keebio/iris-case/iris-switch-plate_left.dxf

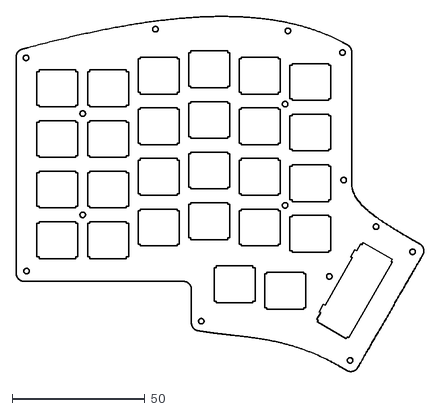
[picture p18: CAD file, 2018-07-17]
iris-switch-plate_left.dxf
153.5 x 133.7
