keebio/iris-case/rev2-only/Iris Middle Tented - Two Piece.stl

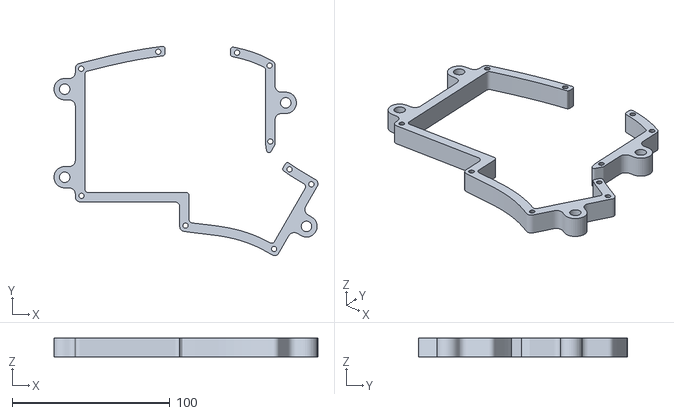
[picture p19: CAD file, 2018-10-11]
rev2-only/Iris Middle Tented - Two Piece.stl
167.2 x 132.5 x 12.0
