keebio/iris-case/phoenix-edition-PE/Iris PE Top Shell for 1.5mm plate.stl

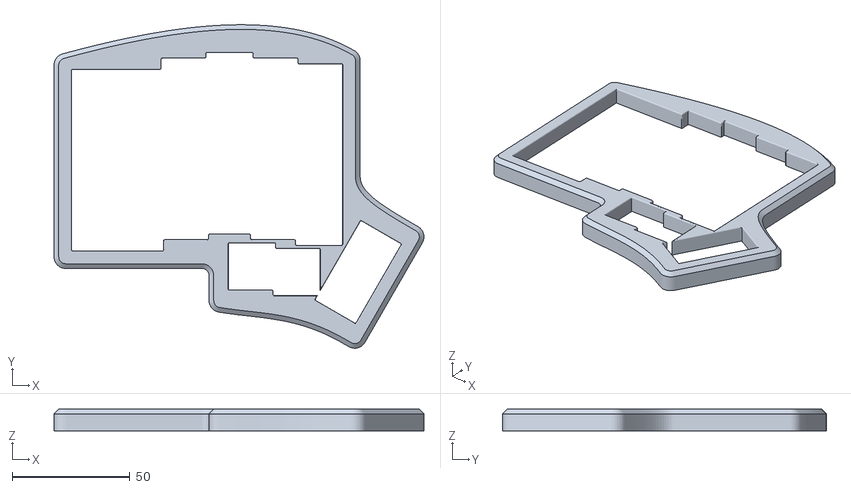
[picture p20: CAD file, 2022-03-10]
phoenix-edition-PE/Iris PE Top Shell for 1.5mm plate.stl
157.4 x 137.7 x 9.30
