keebio/iris-case/rev2-only/Iris R2 Middle Layer - Two Piece.stl

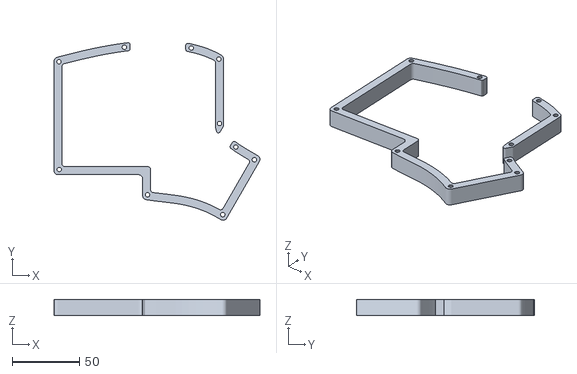
[picture p21: CAD file, 2018-10-11]
rev2-only/Iris R2 Middle Layer - Two Piece.stl
153.7 x 132.5 x 12.0
