keebio/iris-case/rev2-only/iris-rev2-bottom_right.dxf

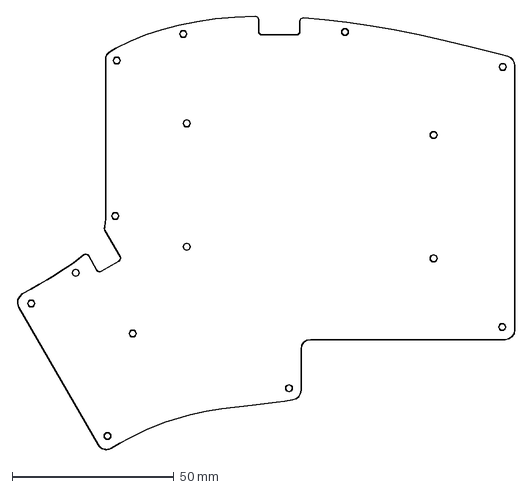
[picture p23: CAD file, 2018-07-17]
rev2-only/iris-rev2-bottom_right.dxf
153.9 x 133.7 mm
