keebio/iris-case/phoenix-edition-PE/Iris PE Middle Layer - Ergodox Tent Kit for 1.5mm Plate.stl

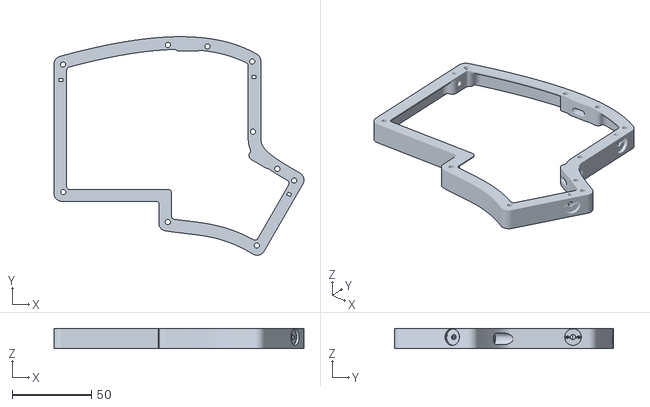
[picture p24: CAD file, 2021-11-29]
phoenix-edition-PE/Iris PE Middle Layer - Ergodox Tent Kit for 1.5mm Plate.stl
157.4 x 137.7 x 12.8
