keebio/iris-case/rev2-only/iris-rev2-bottom_left.dxf

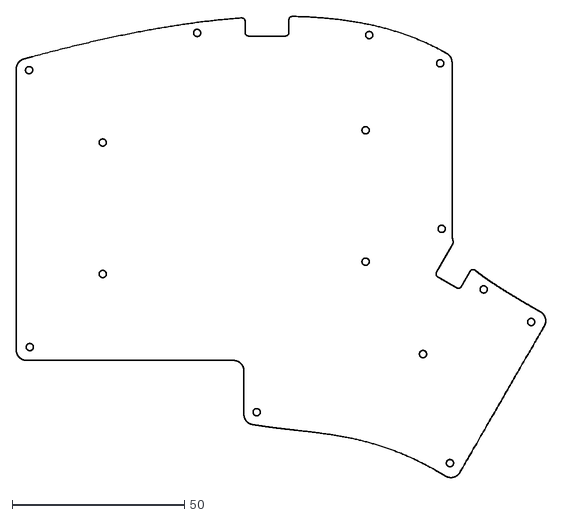
[picture p25: CAD file, 2018-07-17]
rev2-only/iris-rev2-bottom_left.dxf
153.5 x 133.7
