keebio/iris-case/rev3-and-rev4/Iris R3 Middle Layer - Tented for 1.5mm Plate.stl

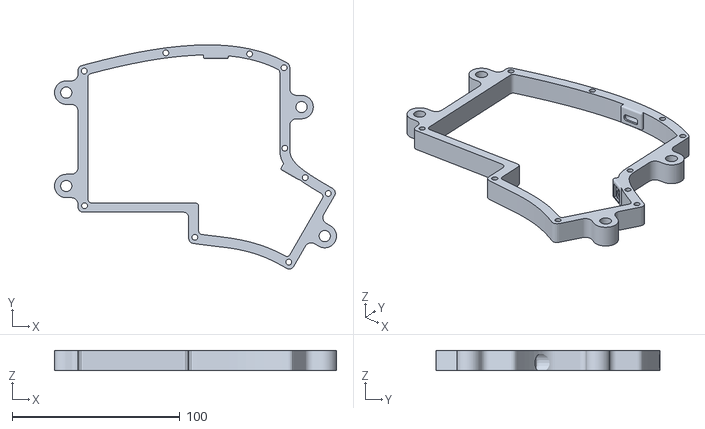
[picture p26: CAD file, 2019-07-23]
rev3-and-rev4/Iris R3 Middle Layer - Tented for 1.5mm Plate.stl
168.1 x 133.7 x 12.0
