keebio/iris-case/phoenix-edition-PE/Iris PE Middle Layer - Normal for 3mm Plate.stl

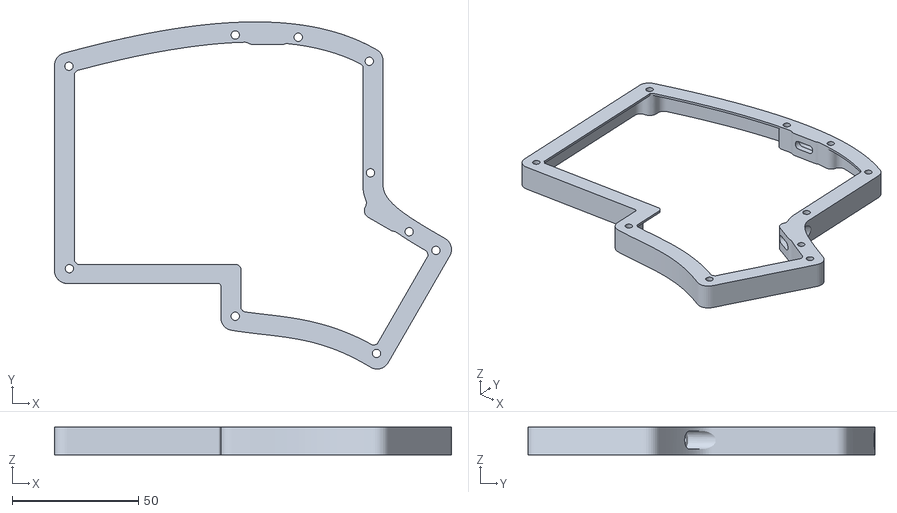
[picture p28: CAD file, 2021-11-19]
phoenix-edition-PE/Iris PE Middle Layer - Normal for 3mm Plate.stl
157.4 x 137.7 x 11.0
