keebio/iris-case/phoenix-edition-PE/Iris PE Middle Layer - Normal for 1.5mm Plate.stl

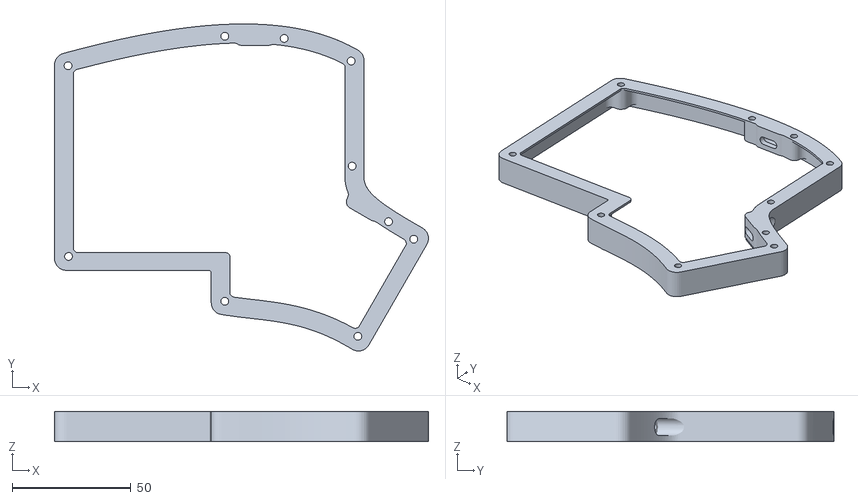
[picture p29: CAD file, 2021-11-19]
phoenix-edition-PE/Iris PE Middle Layer - Normal for 1.5mm Plate.stl
157.4 x 137.7 x 12.8
