keebio/iris-case/rev3-and-rev4/Iris R3 Middle Layer - 2 Piece.stl

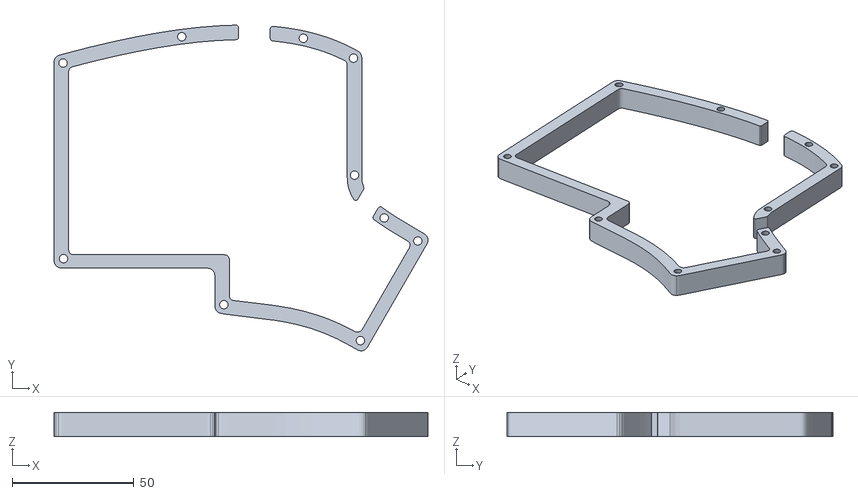
[picture p30: CAD file, 2019-06-10]
rev3-and-rev4/Iris R3 Middle Layer - 2 Piece.stl
153.4 x 133.7 x 10.0
