keebio/iris-case/phoenix-edition-PE/iris-PE-switch-plate-choc.dxf

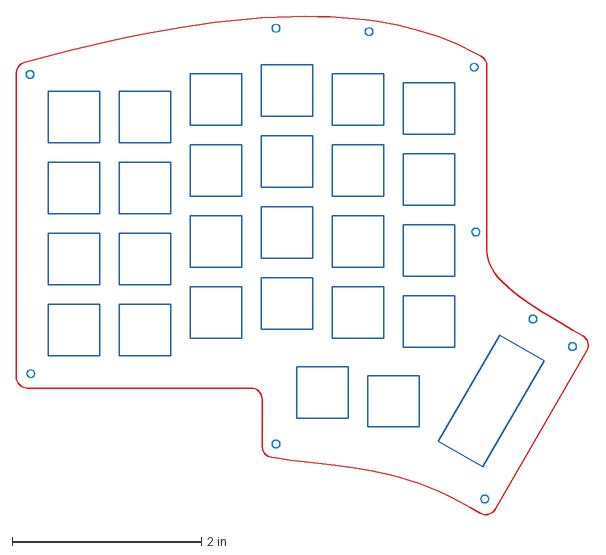
[picture p31: CAD file, 2021-09-30]
phoenix-edition-PE/iris-PE-switch-plate-choc.dxf
6.06 x 5.26 in
