keebio/iris-case/phoenix-edition-PE/iris-PE-switch-plate-mx-alps-3mm.dxf

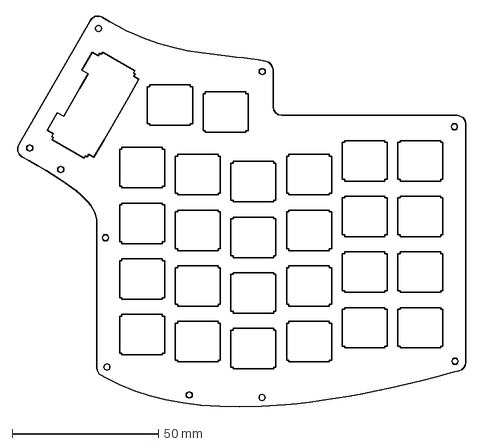
[picture p32: CAD file, 2021-09-30]
phoenix-edition-PE/iris-PE-switch-plate-mx-alps-3mm.dxf
153.9 x 133.7 mm
