keebio/iris-case/phoenix-edition-PE/iris-PE-mid-tented.dxf

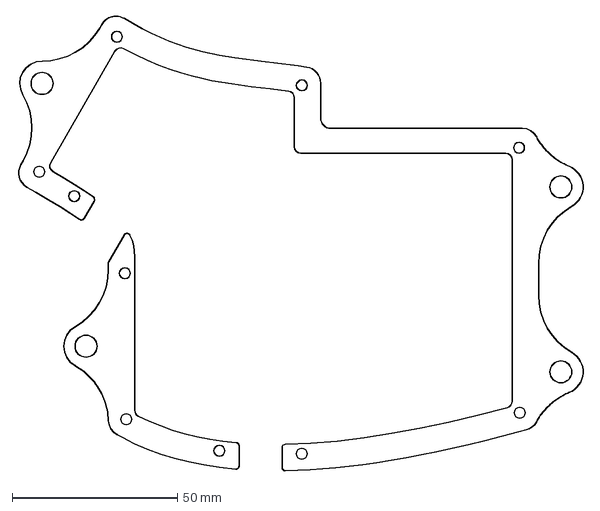
[picture p33: CAD file, 2021-08-18]
phoenix-edition-PE/iris-PE-mid-tented.dxf
171.8 x 137.7 mm
