keebio/iris-case/phoenix-edition-PE/iris-PE-bottom-plate.dxf

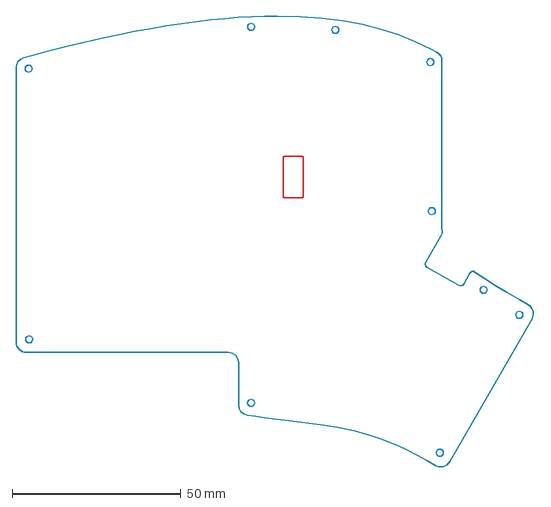
[picture p34: CAD file, 2021-08-18]
phoenix-edition-PE/iris-PE-bottom-plate.dxf
153.9 x 133.7 mm
