keebio/iris-case/phoenix-edition-PE/iris-PE-switch-plate-mx-alps.dxf

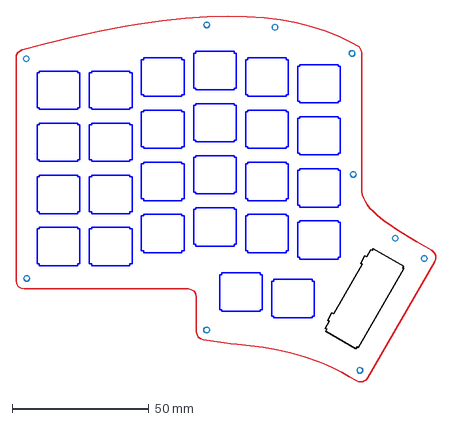
[picture p35: CAD file, 2021-08-18]
phoenix-edition-PE/iris-PE-switch-plate-mx-alps.dxf
153.9 x 133.7 mm
