keebio/iris-case/phoenix-edition-PE/iris-PE-mid-normal.dxf

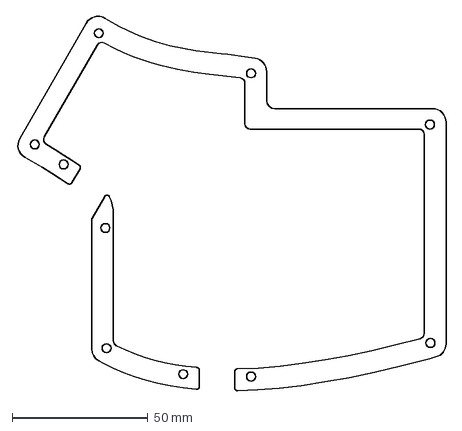
[picture p36: CAD file, 2021-08-18]
phoenix-edition-PE/iris-PE-mid-normal.dxf
158.2 x 137.7 mm
